thomasstadel/AirFleet/sensor/src/L86.h

/*
	@author:  Thomas Stadel
	@date:    2024-11-23
	@brief:   Driver for Queltec L86 GPS module
			  Ref: https://docs.rs-online.com/3824/0900766b8147dbf6.pdf
*/

#ifndef L86_H
#define L86_H

#include "Particle.h"
#include "Settings.h"

class L86 {
	public:
		L86();

		void on();
		void off();
		void loop();
		int8_t getSample(float_t *data, String *datetime);
		void reset_distance();

	private:
		void writeToDevice(uint8_t *buf, size_t len);
		void readFromDevice(uint8_t *buf, size_t len);
		uint16_t parseSample(uint8_t *buf, size_t offset);
		String appendCRC(String str);
		String calcCRC(String str);
		String trim(String str);
		String getPart(String str, int part);
		String readBuffer;
		double_t gps_latitude;
		double_t gps_longitude;
		double_t gps_prev_latitude;
		double_t gps_prev_longitude;
		float_t gps_speed;
		float_t gps_distance;
		uint8_t gps_valid;
		unsigned long gps_millis;
		String gps_datetime;
		float_t calcDecimalDegrees(String str);
		void reset();
};

#endif
